ZackFreedman/Big-Wheel/Wiring Diagram.sch

## EAGLE design Wiring Diagram.sch (2020-11-19)

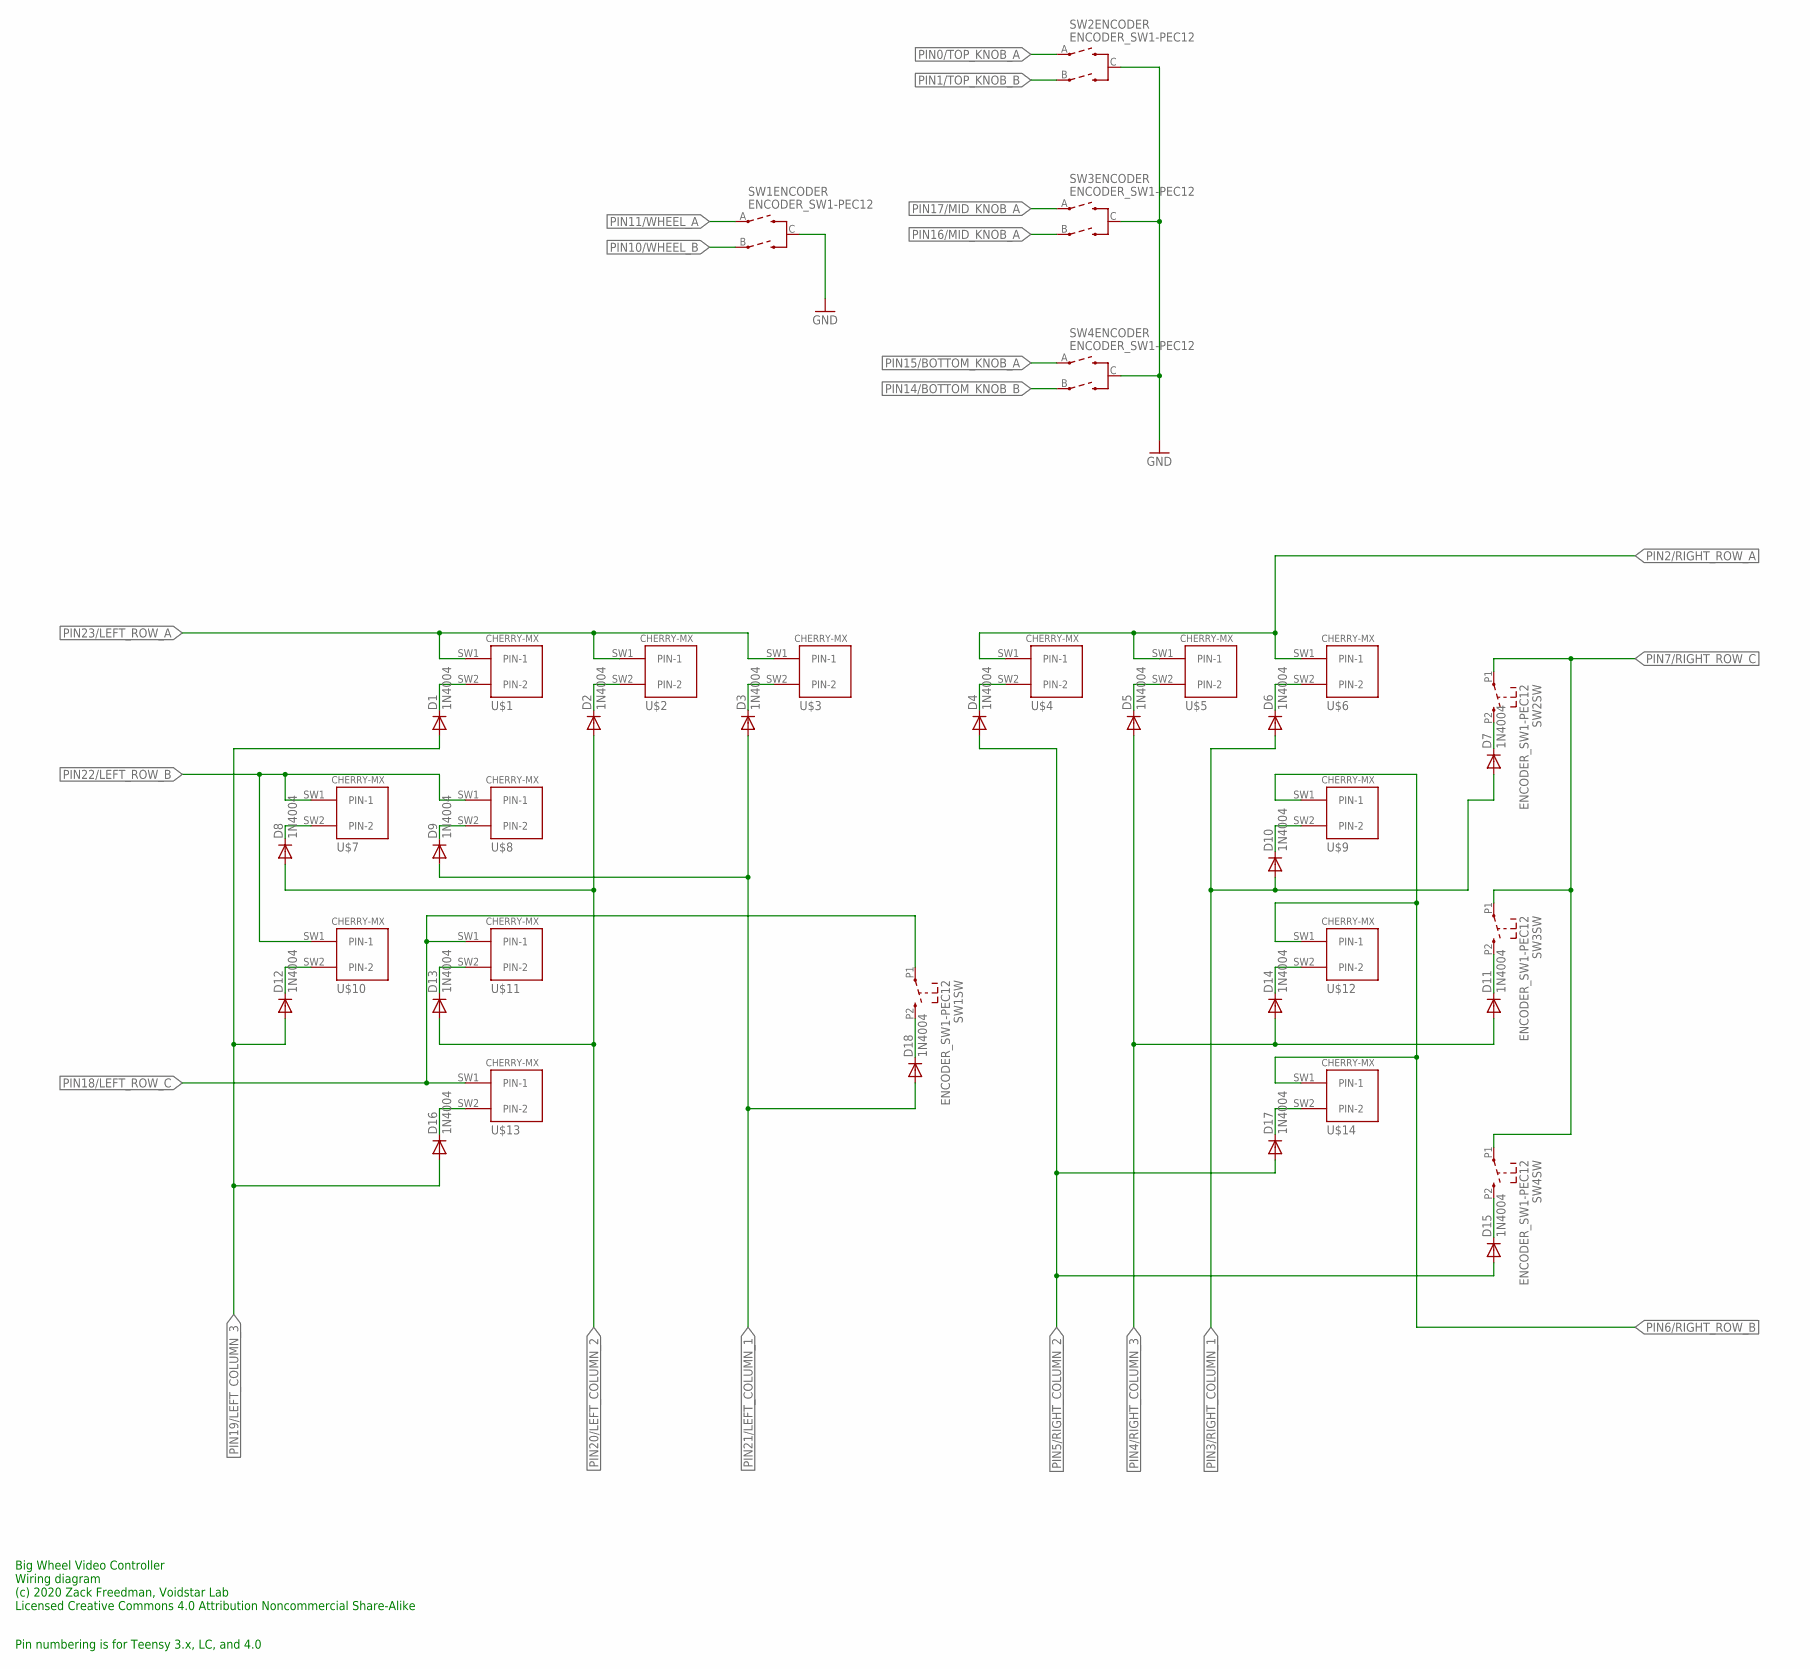
[picture p8: schematic Wiring Diagram.sch]

Parts:
D1, D2, D3, D4, D5, D6, D7, D8, D9, D10, D11, D12, D13, D14, D15, D16, D17, D18: 1N4004; DO41-10
SW1, SW2, SW3, SW4: ENCODER_SW1-PEC12; PEC12_INCREMENTAL_ENCODER
U$1, U$2, U$3, U$4, U$5, U$6, U$7, U$8, U$9, U$10, U$11, U$12, U$13, U$14: CHERRY-MX

Connections:
GND: SW1.C, SW2.C, SW3.C, SW4.C
unnamed: D1.C, U$1.SW2 (PIN-2)
unnamed: D2.C, U$2.SW2 (PIN-2)
unnamed: D3.C, U$3.SW2 (PIN-2)
unnamed: D10.C, U$9.SW2 (PIN-2)
unnamed: D9.C, U$8.SW2 (PIN-2)
unnamed: D18.C, SW1.P2 (2)
unnamed: D12.C, U$10.SW2 (PIN-2)
unnamed: D16.C, U$13.SW2 (PIN-2)
unnamed: D8.C, U$7.SW2 (PIN-2)
unnamed: D13.C, U$11.SW2 (PIN-2)
unnamed: D6.C, U$6.SW2 (PIN-2)
unnamed: D7.C, SW2.P2 (2)
unnamed: D11.C, SW3.P2 (2)
unnamed: D15.C, SW4.P2 (2)
unnamed: D17.C, U$14.SW2 (PIN-2)
unnamed: D14.C, U$12.SW2 (PIN-2)
unnamed: D5.C, U$5.SW2 (PIN-2)
unnamed: D4.C, U$4.SW2 (PIN-2)
PIN0/TOP_KNOB_A: SW2.A
PIN1/TOP_KNOB_B: SW2.B
PIN2/RIGHT_ROW_A: U$4.SW1 (PIN-1), U$5.SW1 (PIN-1), U$6.SW1 (PIN-1)
PIN3/RIGHT_COLUMN_1: D6.A, D7.A, D10.A
PIN4/RIGHT_COLUMN_3: D5.A, D11.A, D14.A
PIN5/RIGHT_COLUMN_2: D4.A, D15.A, D17.A
PIN6/RIGHT_ROW_B: U$9.SW1 (PIN-1), U$12.SW1 (PIN-1), U$14.SW1 (PIN-1)
PIN7/RIGHT_ROW_C: SW2.P1 (1), SW3.P1 (1), SW4.P1 (1)
PIN10/WHEEL_B: SW1.B
PIN11/WHEEL_A: SW1.A
PIN14/BOTTOM_KNOB_B: SW4.B
PIN15/BOTTOM_KNOB_A: SW4.A
PIN16/MID_KNOB_A: SW3.B
PIN17/MID_KNOB_A: SW3.A
PIN18/LEFT_ROW_C: SW1.P1 (1), U$11.SW1 (PIN-1), U$13.SW1 (PIN-1)
PIN19/LEFT_COLUMN_3: D1.A, D12.A, D16.A
PIN20/LEFT_COLUMN_2: D2.A, D8.A, D13.A
PIN21/LEFT_COLUMN_1: D3.A, D9.A, D18.A
PIN22/LEFT_ROW_B: U$7.SW1 (PIN-1), U$8.SW1 (PIN-1), U$10.SW1 (PIN-1)
PIN23/LEFT_ROW_A: U$1.SW1 (PIN-1), U$2.SW1 (PIN-1), U$3.SW1 (PIN-1)

Notes on the sheet:
Big Wheel Video Controller Wiring diagram (c) 2020 Zack Freedman, Voidstar Lab Licensed Creative Commons 4.0 Attribution Noncommercial Share-Alike
Pin numbering is for Teensy 3.x, LC, and 4.0
